ss-builds/FM-Direct-Transmitter/LTSpice Sims/BypassCapTesting.asc

AC1: voltage; ""; AC 1
CShunt: cap; {Cshunt}
CVarac: cap; 5p
R1: res; 1k
R2: res; 12k
R3: res; 10000k
V1: voltage; 1.2
Named nets: 0
.ac dec 100 1 1G
.step param Cshunt list 470p 1n 2.2n 4.7n
